SeattleChris/ergo-code/doc/dactyl-motus-6x4-1+3t6.png

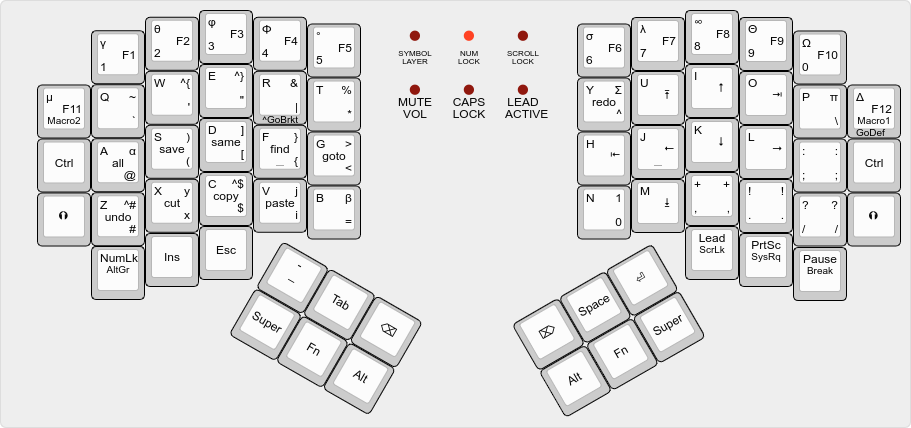
doc/dactyl-motus-6x4-1+3t6.png
