SeattleChris/ergo-code/doc/kb-6col-5row-a.png

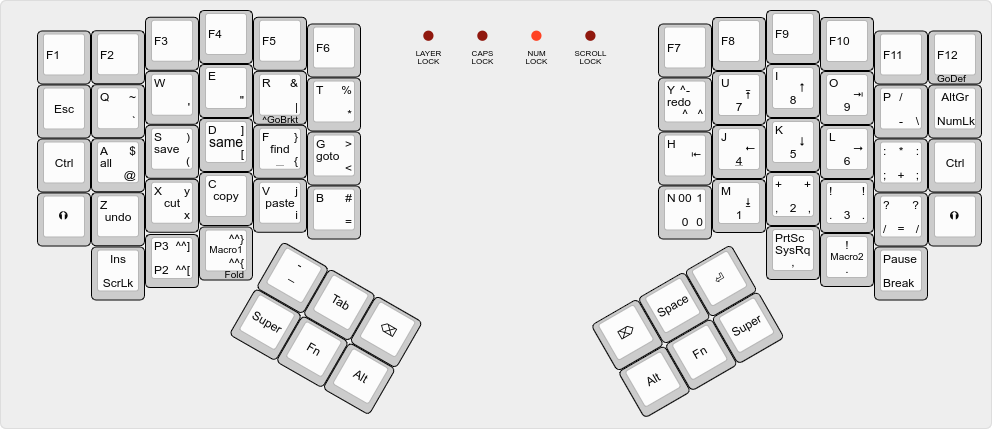
doc/kb-6col-5row-a.png
