SeattleChris/ergo-code/things/test/bowl-4.stl

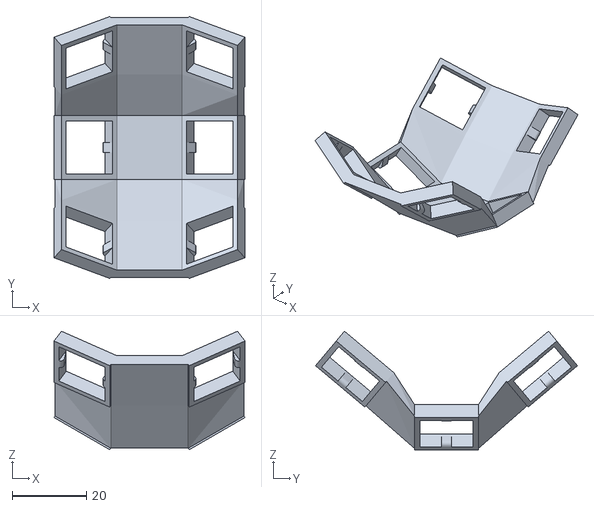
[picture p19: CAD file, 2019-08-27]
things/test/bowl-4.stl
51.5 x 70.7 x 32.0
