SeattleChris/ergo-code/things/chris-2019/right.stl

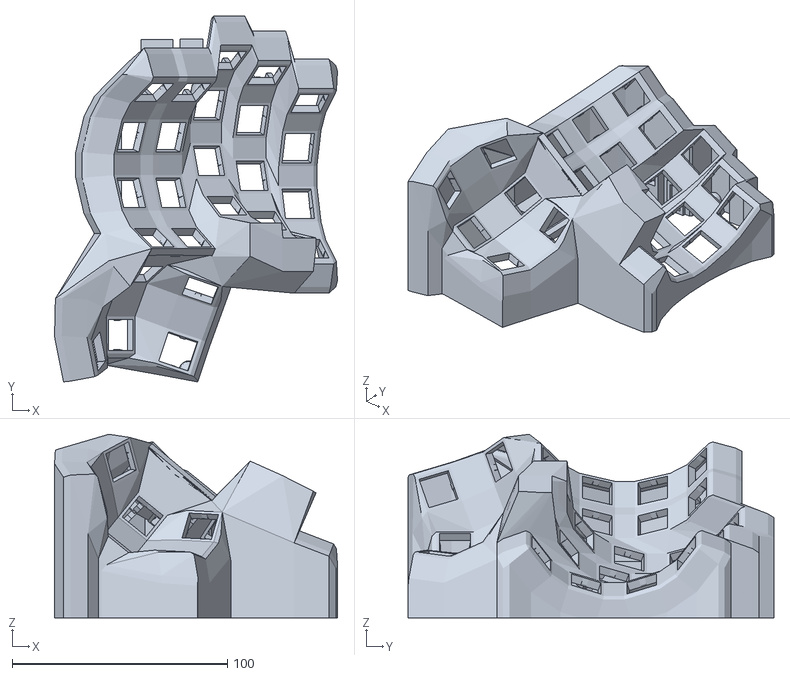
[picture p20: CAD file, 2019-08-27]
things/chris-2019/right.stl
131.4 x 169.8 x 85.2
