SeattleChris/ergo-code/things/right-5x6-plate-ready-to-cut.dxf

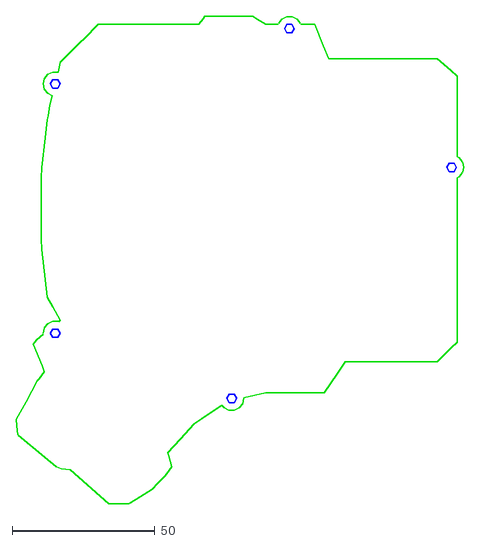
[picture p21: CAD file, 2019-08-27]
things/right-5x6-plate-ready-to-cut.dxf
156.5 x 170.5
