SeattleChris/ergo-code/things/test/thumb-6button.stl

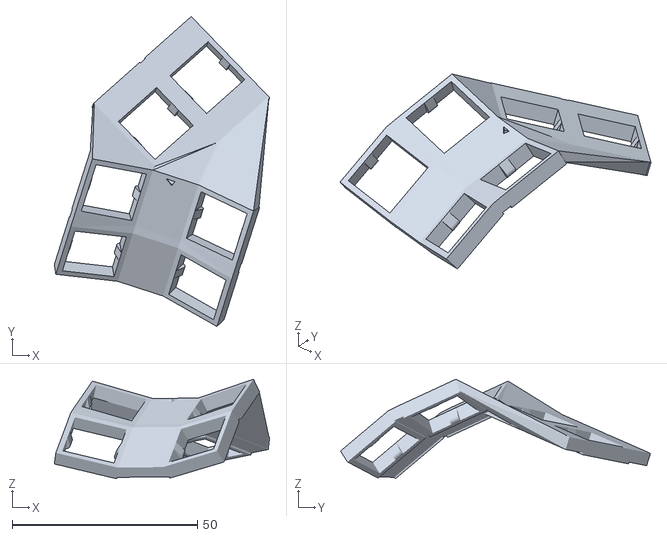
[picture p22: CAD file, 2019-08-27]
things/test/thumb-6button.stl
58.2 x 83.7 x 26.9
