SeattleChris/ergo-code/things/chris-2019/no-num-right.stl

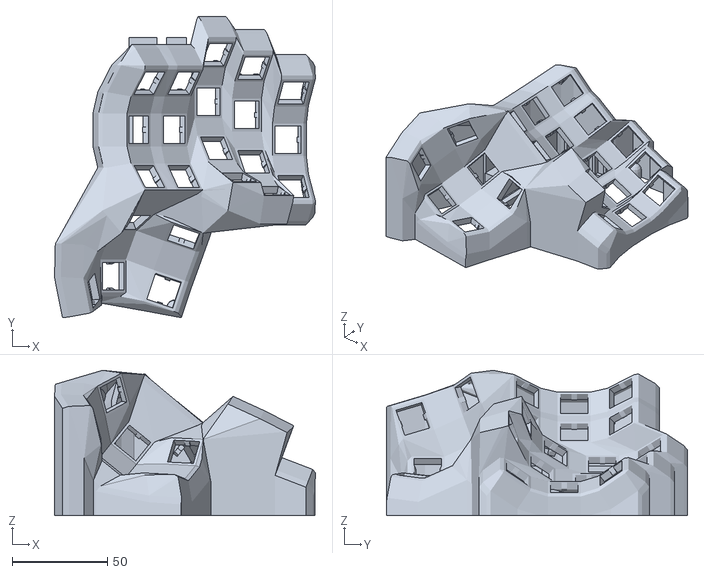
[picture p23: CAD file, 2019-08-27]
things/chris-2019/no-num-right.stl
136.8 x 157.9 x 76.2
