SeattleChris/ergo-code/things/right-4x6.stl

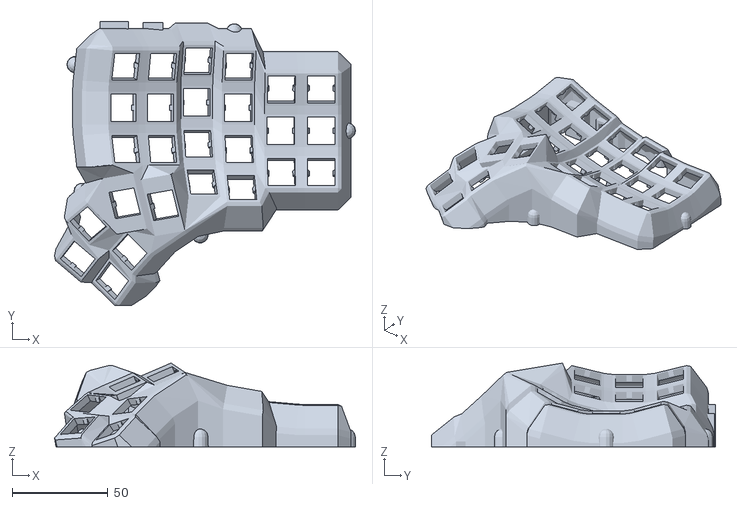
[picture p24: CAD file, 2019-08-27]
things/right-4x6.stl
157.2 x 148.4 x 43.8
