SeattleChris/ergo-code/things/test/thumb-sled1.stl

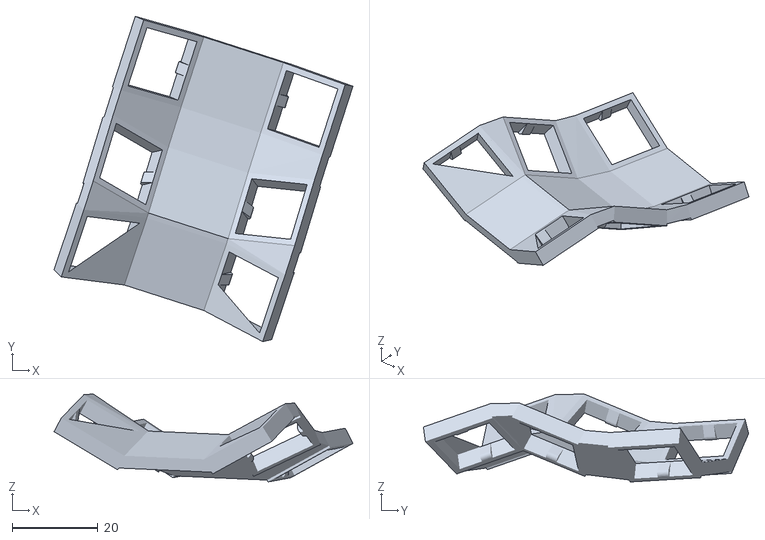
[picture p25: CAD file, 2019-08-27]
things/test/thumb-sled1.stl
69.9 x 76.1 x 20.6
