SeattleChris/ergo-code/things/right-6x6-plate.dxf

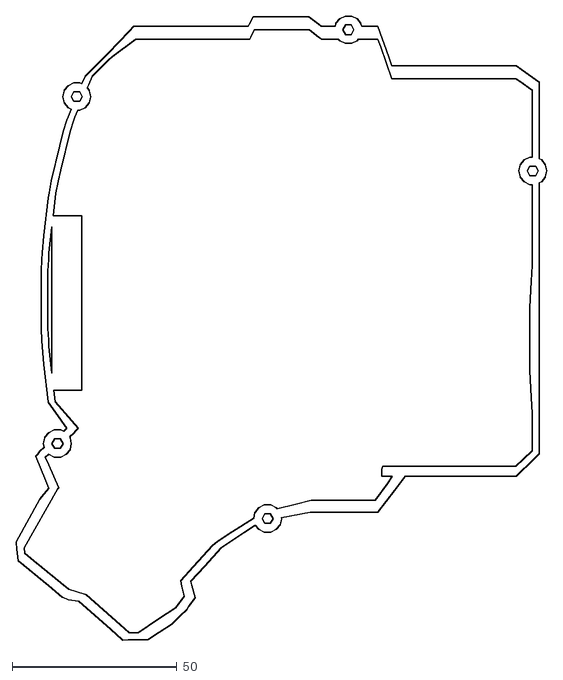
[picture p26: CAD file, 2019-08-27]
things/right-6x6-plate.dxf
160.9 x 189.3
