SeattleChris/ergo-code/things/left-5x6.stl

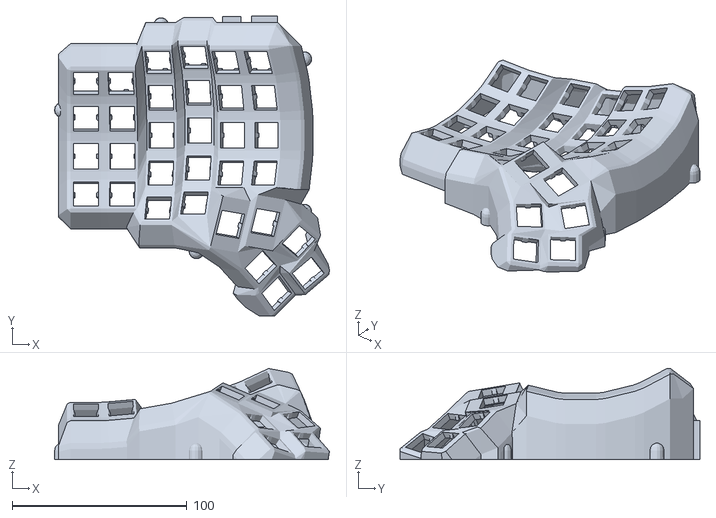
[picture p27: CAD file, 2019-08-27]
things/left-5x6.stl
157.2 x 171.5 x 52.1
