SeattleChris/ergo-code/things/test-lower-thumb.stl

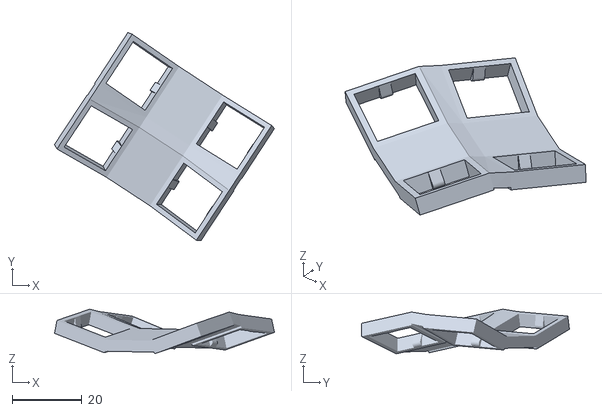
[picture p28: CAD file, 2019-08-27]
things/test-lower-thumb.stl
63.0 x 59.6 x 12.8
