SeattleChris/ergo-code/things/right-4x6-plate.dxf

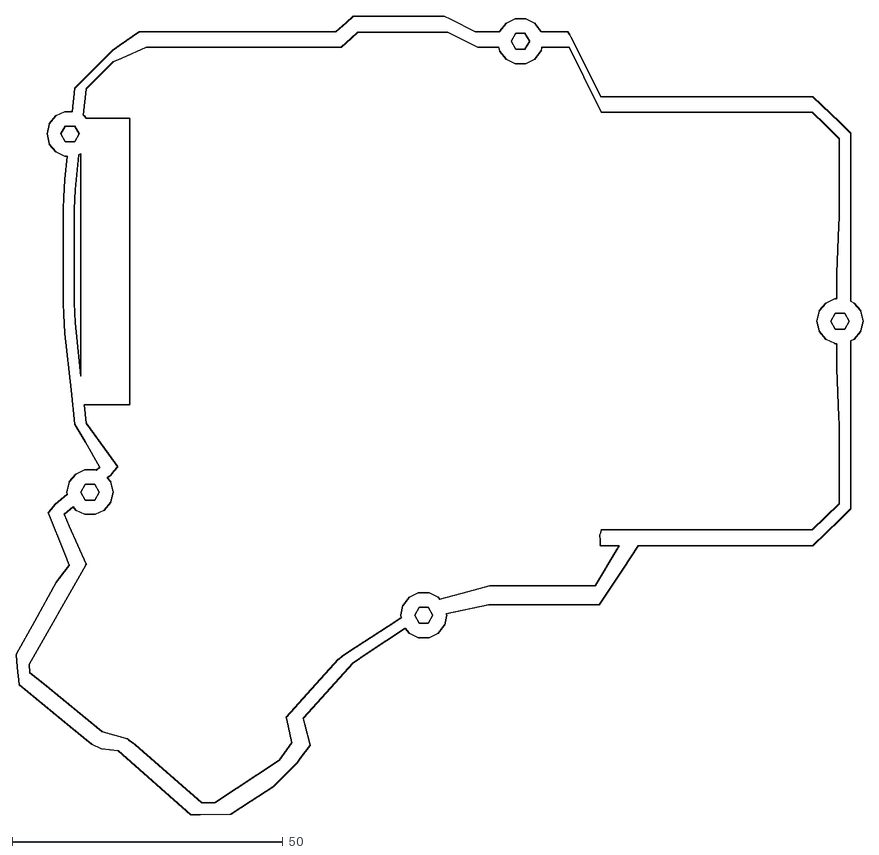
[picture p29: CAD file, 2019-08-27]
things/right-4x6-plate.dxf
156.5 x 147.5
