SeattleChris/ergo-code/things/right-4x5-plate.dxf

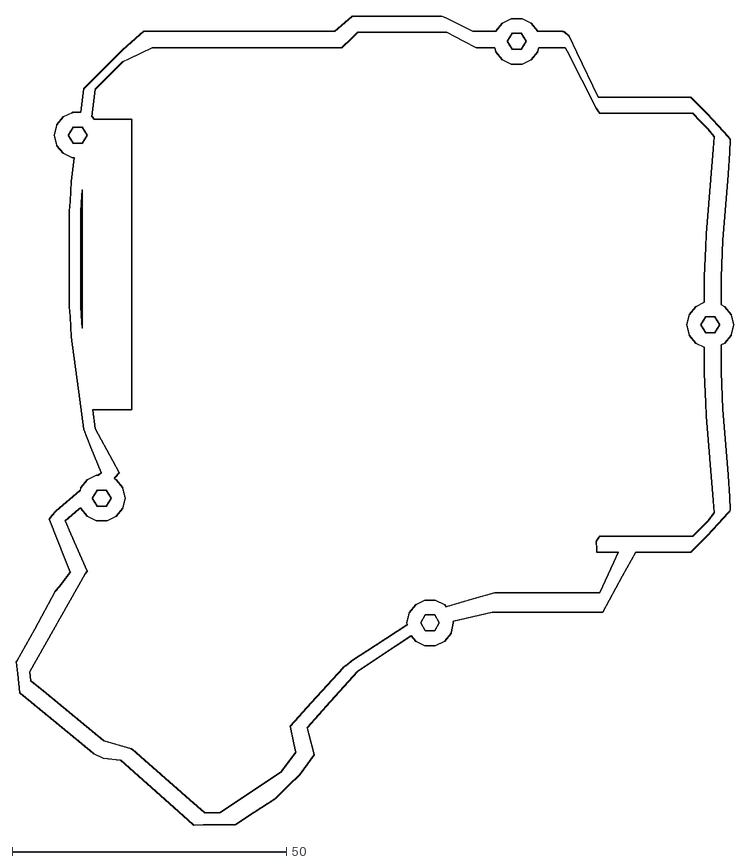
[picture p30: CAD file, 2019-08-27]
things/right-4x5-plate.dxf
130.7 x 147.5
