SeattleChris/ergo-code/things/thumbpad.scad

translate ([0, 0, 8.575]) {
  rotate (a=-40.0, v=[1, 0, 0]) {
    rotate (a=25.0, v=[0, 1, 0]) {
      rotate (a=45.0, v=[0, 0, 1]) {
        rotate (a=-2.5, v=[0, 0, -1]) {
          rotate (a=-59.99999999999999, v=[-1, 0, 0]) {
            rotate (a=-10.0, v=[0, -1, 0]) {
              rotate (a=90.0, v=[0, -1, 0]) {
                rotate (a=90.0, v=[0, 0, 1]) {
                  translate ([35.53437091381005, 63.967580874674, -48.640984358451476]) {
                    union () {
                      union () {
                        union () {
                          translate ([-35.53437091381005, -63.967580874674, 48.640984358451476]) {
                            rotate (a=-2.5, v=[0, 0, 1]) {
                              rotate (a=-10.0, v=[0, 1, 0]) {
                                rotate (a=-59.99999999999999, v=[1, 0, 0]) {
                                  rotate (a=90.0, v=[0, 0, -1]) {
                                    rotate (a=90.0, v=[0, 1, 0]) {
                                      translate ([-8.575, 0, 0]) {
                                        translate ([-9.302129731774905, 0, 0]) {
                                          rotate (a=0.0, v=[1, 0, 0]) {
                                            rotate (a=30.00000000000001, v=[0, 1, 0]) {
                                              union () {
                                                union () {
                                                  translate ([0, 7.825, 1.75]) {
                                                    cube ([17.15, 1.5, 3.5], center=true);
                                                  }
                                                  translate ([7.825, 0, 1.75]) {
                                                    cube ([1.5, 17.15, 3.5], center=true);
                                                  }
                                                  hull () {
                                                    translate ([7.825, 0, 1.75]) {
                                                      cube ([1.5, 2.75, 3.5], center=true);
                                                    }
                                                    translate ([7.075, 0, 1]) {
                                                      rotate (a=90.0, v=[1, 0, 0]) {
                                                        cylinder ($fn=30, h=2.75, r=0, center=true);
                                                      }
                                                    }
                                                  }
                                                }
                                                mirror ([0, 1, 0]) {
                                                  mirror ([1, 0, 0]) {
                                                    union () {
                                                      translate ([0, 7.825, 1.75]) {
                                                        cube ([17.15, 1.5, 3.5], center=true);
                                                      }
                                                      translate ([7.825, 0, 1.75]) {
                                                        cube ([1.5, 17.15, 3.5], center=true);
                                                      }
                                                      hull () {
                                                        translate ([7.825, 0, 1.75]) {
                                                          cube ([1.5, 2.75, 3.5], center=true);
                                                        }
                                                        translate ([7.075, 0, 1]) {
                                                          rotate (a=90.0, v=[1, 0, 0]) {
                                                            cylinder ($fn=30, h=2.75, r=0, center=true);
                                                          }
                                                        }
                                                      }
                                                    }
                                                  }
                                                }
                                              }
                                            }
                                          }
                                        }
                                      }
                                    }
                                  }
                                }
                              }
                            }
                          }
                          translate ([-35.53437091381005, -63.967580874674, 48.640984358451476]) {
                            rotate (a=-2.5, v=[0, 0, 1]) {
                              rotate (a=-10.0, v=[0, 1, 0]) {
                                rotate (a=-59.99999999999999, v=[1, 0, 0]) {
                                  rotate (a=90.0, v=[0, 0, -1]) {
                                    rotate (a=90.0, v=[0, 1, 0]) {
                                      translate ([8.575, 0, 0]) {
                                        translate ([9.302129731774905, 0, 0]) {
                                          rotate (a=0.0, v=[1, 0, 0]) {
                                            rotate (a=30.00000000000001, v=[0, -1, 0]) {
                                              union () {
                                                union () {
                                                  translate ([0, 7.825, 1.75]) {
                                                    cube ([17.15, 1.5, 3.5], center=true);
                                                  }
                                                  translate ([7.825, 0, 1.75]) {
                                                    cube ([1.5, 17.15, 3.5], center=true);
                                                  }
                                                  hull () {
                                                    translate ([7.825, 0, 1.75]) {
                                                      cube ([1.5, 2.75, 3.5], center=true);
                                                    }
                                                    translate ([7.075, 0, 1]) {
                                                      rotate (a=90.0, v=[1, 0, 0]) {
                                                        cylinder ($fn=30, h=2.75, r=0, center=true);
                                                      }
                                                    }
                                                  }
                                                }
                                                mirror ([0, 1, 0]) {
                                                  mirror ([1, 0, 0]) {
                                                    union () {
                                                      translate ([0, 7.825, 1.75]) {
                                                        cube ([17.15, 1.5, 3.5], center=true);
                                                      }
                                                      translate ([7.825, 0, 1.75]) {
                                                        cube ([1.5, 17.15, 3.5], center=true);
                                                      }
                                                      hull () {
                                                        translate ([7.825, 0, 1.75]) {
                                                          cube ([1.5, 2.75, 3.5], center=true);
                                                        }
                                                        translate ([7.075, 0, 1]) {
                                                          rotate (a=90.0, v=[1, 0, 0]) {
                                                            cylinder ($fn=30, h=2.75, r=0, center=true);
                                                          }
                                                        }
                                                      }
                                                    }
                                                  }
                                                }
                                              }
                                            }
                                          }
                                        }
                                      }
                                    }
                                  }
                                }
                              }
                            }
                          }
                          translate ([-35.53437091381005, -63.967580874674, 48.640984358451476]) {
                            rotate (a=-2.5, v=[0, 0, 1]) {
                              rotate (a=-10.0, v=[0, 1, 0]) {
                                rotate (a=-59.99999999999999, v=[1, 0, 0]) {
                                  rotate (a=90.0, v=[0, 0, -1]) {
                                    rotate (a=90.0, v=[0, 1, 0]) {
                                      translate ([0, -13.177145998574055, 15.70391108393905]) {
                                        translate ([-8.575, -12.149999999999999, 0]) {
                                          translate ([-9.302129731774905, 0, 0]) {
                                            rotate (a=-40.0, v=[1, 0, 0]) {
                                              rotate (a=30.00000000000001, v=[0, 1, 0]) {
                                                union () {
                                                  union () {
                                                    translate ([0, 7.825, 1.75]) {
                                                      cube ([17.15, 1.5, 3.5], center=true);
                                                    }
                                                    translate ([7.825, 0, 1.75]) {
                                                      cube ([1.5, 17.15, 3.5], center=true);
                                                    }
                                                    hull () {
                                                      translate ([7.825, 0, 1.75]) {
                                                        cube ([1.5, 2.75, 3.5], center=true);
                                                      }
                                                      translate ([7.075, 0, 1]) {
                                                        rotate (a=90.0, v=[1, 0, 0]) {
                                                          cylinder ($fn=30, h=2.75, r=0, center=true);
                                                        }
                                                      }
                                                    }
                                                  }
                                                  mirror ([0, 1, 0]) {
                                                    mirror ([1, 0, 0]) {
                                                      union () {
                                                        translate ([0, 7.825, 1.75]) {
                                                          cube ([17.15, 1.5, 3.5], center=true);
                                                        }
                                                        translate ([7.825, 0, 1.75]) {
                                                          cube ([1.5, 17.15, 3.5], center=true);
                                                        }
                                                        hull () {
                                                          translate ([7.825, 0, 1.75]) {
                                                            cube ([1.5, 2.75, 3.5], center=true);
                                                          }
                                                          translate ([7.075, 0, 1]) {
                                                            rotate (a=90.0, v=[1, 0, 0]) {
                                                              cylinder ($fn=30, h=2.75, r=0, center=true);
                                                            }
                                                          }
                                                        }
                                                      }
                                                    }
                                                  }
                                                }
                                              }
                                            }
                                          }
                                        }
                                      }
                                    }
                                  }
                                }
                              }
                            }
                          }
                          translate ([-35.53437091381005, -63.967580874674, 48.640984358451476]) {
                            rotate (a=-2.5, v=[0, 0, 1]) {
                              rotate (a=-10.0, v=[0, 1, 0]) {
                                rotate (a=-59.99999999999999, v=[1, 0, 0]) {
                                  rotate (a=90.0, v=[0, 0, -1]) {
                                    rotate (a=90.0, v=[0, 1, 0]) {
                                      translate ([0, -13.177145998574055, 15.70391108393905]) {
                                        translate ([8.575, -12.149999999999999, 0]) {
                                          translate ([9.302129731774905, 0, 0]) {
                                            rotate (a=-40.0, v=[1, 0, 0]) {
                                              rotate (a=30.00000000000001, v=[0, -1, 0]) {
                                                union () {
                                                  union () {
                                                    translate ([0, 7.825, 1.75]) {
                                                      cube ([17.15, 1.5, 3.5], center=true);
                                                    }
                                                    translate ([7.825, 0, 1.75]) {
                                                      cube ([1.5, 17.15, 3.5], center=true);
                                                    }
                                                    hull () {
                                                      translate ([7.825, 0, 1.75]) {
                                                        cube ([1.5, 2.75, 3.5], center=true);
                                                      }
                                                      translate ([7.075, 0, 1]) {
                                                        rotate (a=90.0, v=[1, 0, 0]) {
                                                          cylinder ($fn=30, h=2.75, r=0, center=true);
                                                        }
                                                      }
                                                    }
                                                  }
                                                  mirror ([0, 1, 0]) {
                                                    mirror ([1, 0, 0]) {
                                                      union () {
                                                        translate ([0, 7.825, 1.75]) {
                                                          cube ([17.15, 1.5, 3.5], center=true);
                                                        }
                                                        translate ([7.825, 0, 1.75]) {
                                                          cube ([1.5, 17.15, 3.5], center=true);
                                                        }
                                                        hull () {
                                                          translate ([7.825, 0, 1.75]) {
                                                            cube ([1.5, 2.75, 3.5], center=true);
                                                          }
                                                          translate ([7.075, 0, 1]) {
                                                            rotate (a=90.0, v=[1, 0, 0]) {
                                                              cylinder ($fn=30, h=2.75, r=0, center=true);
                                                            }
                                                          }
                                                        }
                                                      }
                                                    }
                                                  }
                                                }
                                              }
                                            }
                                          }
                                        }
                                      }
                                    }
                                  }
                                }
                              }
                            }
                          }
                        }
                        union () {
                          translate ([-35.53437091381005, -63.967580874674, 48.640984358451476]) {
                            rotate (a=-2.5, v=[0, 0, 1]) {
                              rotate (a=-10.0, v=[0, 1, 0]) {
                                rotate (a=-59.99999999999999, v=[1, 0, 0]) {
                                  rotate (a=90.0, v=[0, 0, -1]) {
                                    rotate (a=90.0, v=[0, 1, 0]) {
                                      translate ([0, 13.177145998574055, 15.70391108393905]) {
                                        translate ([-8.575, 12.149999999999999, 0]) {
                                          translate ([-9.302129731774905, 0, 0]) {
                                            rotate (a=40.0, v=[1, 0, 0]) {
                                              rotate (a=30.00000000000001, v=[0, 1, 0]) {
                                                union () {
                                                  union () {
                                                    translate ([0, 7.825, 1.75]) {
                                                      cube ([17.15, 1.5, 3.5], center=true);
                                                    }
                                                    translate ([7.825, 0, 1.75]) {
                                                      cube ([1.5, 17.15, 3.5], center=true);
                                                    }
                                                    hull () {
                                                      translate ([7.825, 0, 1.75]) {
                                                        cube ([1.5, 2.75, 3.5], center=true);
                                                      }
                                                      translate ([7.075, 0, 1]) {
                                                        rotate (a=90.0, v=[1, 0, 0]) {
                                                          cylinder ($fn=30, h=2.75, r=0, center=true);
                                                        }
                                                      }
                                                    }
                                                  }
                                                  mirror ([0, 1, 0]) {
                                                    mirror ([1, 0, 0]) {
                                                      union () {
                                                        translate ([0, 7.825, 1.75]) {
                                                          cube ([17.15, 1.5, 3.5], center=true);
                                                        }
                                                        translate ([7.825, 0, 1.75]) {
                                                          cube ([1.5, 17.15, 3.5], center=true);
                                                        }
                                                        hull () {
                                                          translate ([7.825, 0, 1.75]) {
                                                            cube ([1.5, 2.75, 3.5], center=true);
                                                          }
                                                          translate ([7.075, 0, 1]) {
                                                            rotate (a=90.0, v=[1, 0, 0]) {
                                                              cylinder ($fn=30, h=2.75, r=0, center=true);
                                                            }
                                                          }
                                                        }
                                                      }
                                                    }
                                                  }
                                                }
                                              }
                                            }
                                          }
                                        }
                                      }
                                    }
                                  }
                                }
                              }
                            }
                          }
                          translate ([-35.53437091381005, -63.967580874674, 48.640984358451476]) {
                            rotate (a=-2.5, v=[0, 0, 1]) {
                              rotate (a=-10.0, v=[0, 1, 0]) {
                                rotate (a=-59.99999999999999, v=[1, 0, 0]) {
                                  rotate (a=90.0, v=[0, 0, -1]) {
                                    rotate (a=90.0, v=[0, 1, 0]) {
                                      translate ([0, 13.177145998574055, 15.70391108393905]) {
                                        translate ([8.575, 12.149999999999999, 0]) {
                                          translate ([9.302129731774905, 0, 0]) {
                                            rotate (a=40.0, v=[1, 0, 0]) {
                                              rotate (a=30.00000000000001, v=[0, -1, 0]) {
                                                union () {
                                                  union () {
                                                    translate ([0, 7.825, 1.75]) {
                                                      cube ([17.15, 1.5, 3.5], center=true);
                                                    }
                                                    translate ([7.825, 0, 1.75]) {
                                                      cube ([1.5, 17.15, 3.5], center=true);
                                                    }
                                                    hull () {
                                                      translate ([7.825, 0, 1.75]) {
                                                        cube ([1.5, 2.75, 3.5], center=true);
                                                      }
                                                      translate ([7.075, 0, 1]) {
                                                        rotate (a=90.0, v=[1, 0, 0]) {
                                                          cylinder ($fn=30, h=2.75, r=0, center=true);
                                                        }
                                                      }
                                                    }
                                                  }
                                                  mirror ([0, 1, 0]) {
                                                    mirror ([1, 0, 0]) {
                                                      union () {
                                                        translate ([0, 7.825, 1.75]) {
                                                          cube ([17.15, 1.5, 3.5], center=true);
                                                        }
                                                        translate ([7.825, 0, 1.75]) {
                                                          cube ([1.5, 17.15, 3.5], center=true);
                                                        }
                                                        hull () {
                                                          translate ([7.825, 0, 1.75]) {
                                                            cube ([1.5, 2.75, 3.5], center=true);
                                                          }
                                                          translate ([7.075, 0, 1]) {
                                                            rotate (a=90.0, v=[1, 0, 0]) {
                                                              cylinder ($fn=30, h=2.75, r=0, center=true);
                                                            }
                                                          }
                                                        }
                                                      }
                                                    }
                                                  }
                                                }
                                              }
                                            }
                                          }
                                        }
                                      }
                                    }
                                  }
                                }
                              }
                            }
                          }
                        }
                      }
                      union () {
                        union () {
                          hull () {
                            translate ([-35.53437091381005, -63.967580874674, 48.640984358451476]) {
                              rotate (a=-2.5, v=[0, 0, 1]) {
                                rotate (a=-10.0, v=[0, 1, 0]) {
                                  rotate (a=-59.99999999999999, v=[1, 0, 0]) {
                                    rotate (a=90.0, v=[0, 0, -1]) {
                                      rotate (a=90.0, v=[0, 1, 0]) {
                                        translate ([0, 13.177145998574055, 15.70391108393905]) {
                                          translate ([-8.575, 12.149999999999999, 0]) {
                                            translate ([-9.302129731774905, 0, 0]) {
                                              rotate (a=40.0, v=[1, 0, 0]) {
                                                rotate (a=30.00000000000001, v=[0, 1, 0]) {
                                                  translate ([8.524999999999999, 8.524999999999999, 0]) {
                                                    translate ([0, 0, 1.75]) {
                                                      cube ([0.1, 0.1, 3.5], center=true);
                                                    }
                                                  }
                                                }
                                              }
                                            }
                                          }
                                        }
                                      }
                                    }
                                  }
                                }
                              }
                            }
                            translate ([-35.53437091381005, -63.967580874674, 48.640984358451476]) {
                              rotate (a=-2.5, v=[0, 0, 1]) {
                                rotate (a=-10.0, v=[0, 1, 0]) {
                                  rotate (a=-59.99999999999999, v=[1, 0, 0]) {
                                    rotate (a=90.0, v=[0, 0, -1]) {
                                      rotate (a=90.0, v=[0, 1, 0]) {
                                        translate ([0, 13.177145998574055, 15.70391108393905]) {
                                          translate ([8.575, 12.149999999999999, 0]) {
                                            translate ([9.302129731774905, 0, 0]) {
                                              rotate (a=40.0, v=[1, 0, 0]) {
                                                rotate (a=30.00000000000001, v=[0, -1, 0]) {
                                                  translate ([-8.524999999999999, 8.524999999999999, 0]) {
                                                    translate ([0, 0, 1.75]) {
                                                      cube ([0.1, 0.1, 3.5], center=true);
                                                    }
                                                  }
                                                }
                                              }
                                            }
                                          }
                                        }
                                      }
                                    }
                                  }
                                }
                              }
                            }
                            translate ([-35.53437091381005, -63.967580874674, 48.640984358451476]) {
                              rotate (a=-2.5, v=[0, 0, 1]) {
                                rotate (a=-10.0, v=[0, 1, 0]) {
                                  rotate (a=-59.99999999999999, v=[1, 0, 0]) {
                                    rotate (a=90.0, v=[0, 0, -1]) {
                                      rotate (a=90.0, v=[0, 1, 0]) {
                                        translate ([0, 13.177145998574055, 15.70391108393905]) {
                                          translate ([-8.575, 12.149999999999999, 0]) {
                                            translate ([-9.302129731774905, 0, 0]) {
                                              rotate (a=40.0, v=[1, 0, 0]) {
                                                rotate (a=30.00000000000001, v=[0, 1, 0]) {
                                                  translate ([8.524999999999999, -8.524999999999999, 0]) {
                                                    translate ([0, 0, 1.75]) {
                                                      cube ([0.1, 0.1, 3.5], center=true);
                                                    }
                                                  }
                                                }
                                              }
                                            }
                                          }
                                        }
                                      }
                                    }
                                  }
                                }
                              }
                            }
                          }
                          hull () {
                            translate ([-35.53437091381005, -63.967580874674, 48.640984358451476]) {
                              rotate (a=-2.5, v=[0, 0, 1]) {
                                rotate (a=-10.0, v=[0, 1, 0]) {
                                  rotate (a=-59.99999999999999, v=[1, 0, 0]) {
                                    rotate (a=90.0, v=[0, 0, -1]) {
                                      rotate (a=90.0, v=[0, 1, 0]) {
                                        translate ([0, 13.177145998574055, 15.70391108393905]) {
                                          translate ([8.575, 12.149999999999999, 0]) {
                                            translate ([9.302129731774905, 0, 0]) {
                                              rotate (a=40.0, v=[1, 0, 0]) {
                                                rotate (a=30.00000000000001, v=[0, -1, 0]) {
                                                  translate ([-8.524999999999999, 8.524999999999999, 0]) {
                                                    translate ([0, 0, 1.75]) {
                                                      cube ([0.1, 0.1, 3.5], center=true);
                                                    }
                                                  }
                                                }
                                              }
                                            }
                                          }
                                        }
                                      }
                                    }
                                  }
                                }
                              }
                            }
                            translate ([-35.53437091381005, -63.967580874674, 48.640984358451476]) {
                              rotate (a=-2.5, v=[0, 0, 1]) {
                                rotate (a=-10.0, v=[0, 1, 0]) {
                                  rotate (a=-59.99999999999999, v=[1, 0, 0]) {
                                    rotate (a=90.0, v=[0, 0, -1]) {
                                      rotate (a=90.0, v=[0, 1, 0]) {
                                        translate ([0, 13.177145998574055, 15.70391108393905]) {
                                          translate ([-8.575, 12.149999999999999, 0]) {
                                            translate ([-9.302129731774905, 0, 0]) {
                                              rotate (a=40.0, v=[1, 0, 0]) {
                                                rotate (a=30.00000000000001, v=[0, 1, 0]) {
                                                  translate ([8.524999999999999, -8.524999999999999, 0]) {
                                                    translate ([0, 0, 1.75]) {
                                                      cube ([0.1, 0.1, 3.5], center=true);
                                                    }
                                                  }
                                                }
                                              }
                                            }
                                          }
                                        }
                                      }
                                    }
                                  }
                                }
                              }
                            }
                            translate ([-35.53437091381005, -63.967580874674, 48.640984358451476]) {
                              rotate (a=-2.5, v=[0, 0, 1]) {
                                rotate (a=-10.0, v=[0, 1, 0]) {
                                  rotate (a=-59.99999999999999, v=[1, 0, 0]) {
                                    rotate (a=90.0, v=[0, 0, -1]) {
                                      rotate (a=90.0, v=[0, 1, 0]) {
                                        translate ([0, 13.177145998574055, 15.70391108393905]) {
                                          translate ([8.575, 12.149999999999999, 0]) {
                                            translate ([9.302129731774905, 0, 0]) {
                                              rotate (a=40.0, v=[1, 0, 0]) {
                                                rotate (a=30.00000000000001, v=[0, -1, 0]) {
                                                  translate ([-8.524999999999999, -8.524999999999999, 0]) {
                                                    translate ([0, 0, 1.75]) {
                                                      cube ([0.1, 0.1, 3.5], center=true);
                                                    }
                                                  }
                                                }
                                              }
                                            }
                                          }
                                        }
                                      }
                                    }
                                  }
                                }
                              }
                            }
                          }
                        }
                        union () {
                          hull () {
                            translate ([-35.53437091381005, -63.967580874674, 48.640984358451476]) {
                              rotate (a=-2.5, v=[0, 0, 1]) {
                                rotate (a=-10.0, v=[0, 1, 0]) {
                                  rotate (a=-59.99999999999999, v=[1, 0, 0]) {
                                    rotate (a=90.0, v=[0, 0, -1]) {
                                      rotate (a=90.0, v=[0, 1, 0]) {
                                        translate ([0, -13.177145998574055, 15.70391108393905]) {
                                          translate ([8.575, -12.149999999999999, 0]) {
                                            translate ([9.302129731774905, 0, 0]) {
                                              rotate (a=-40.0, v=[1, 0, 0]) {
                                                rotate (a=30.00000000000001, v=[0, -1, 0]) {
                                                  translate ([-8.524999999999999, -8.524999999999999, 0]) {
                                                    translate ([0, 0, 1.75]) {
                                                      cube ([0.1, 0.1, 3.5], center=true);
                                                    }
                                                  }
                                                }
                                              }
                                            }
                                          }
                                        }
                                      }
                                    }
                                  }
                                }
                              }
                            }
                            translate ([-35.53437091381005, -63.967580874674, 48.640984358451476]) {
                              rotate (a=-2.5, v=[0, 0, 1]) {
                                rotate (a=-10.0, v=[0, 1, 0]) {
                                  rotate (a=-59.99999999999999, v=[1, 0, 0]) {
                                    rotate (a=90.0, v=[0, 0, -1]) {
                                      rotate (a=90.0, v=[0, 1, 0]) {
                                        translate ([0, -13.177145998574055, 15.70391108393905]) {
                                          translate ([-8.575, -12.149999999999999, 0]) {
                                            translate ([-9.302129731774905, 0, 0]) {
                                              rotate (a=-40.0, v=[1, 0, 0]) {
                                                rotate (a=30.00000000000001, v=[0, 1, 0]) {
                                                  translate ([8.524999999999999, -8.524999999999999, 0]) {
                                                    translate ([0, 0, 1.75]) {
                                                      cube ([0.1, 0.1, 3.5], center=true);
                                                    }
                                                  }
                                                }
                                              }
                                            }
                                          }
                                        }
                                      }
                                    }
                                  }
                                }
                              }
                            }
                            translate ([-35.53437091381005, -63.967580874674, 48.640984358451476]) {
                              rotate (a=-2.5, v=[0, 0, 1]) {
                                rotate (a=-10.0, v=[0, 1, 0]) {
                                  rotate (a=-59.99999999999999, v=[1, 0, 0]) {
                                    rotate (a=90.0, v=[0, 0, -1]) {
                                      rotate (a=90.0, v=[0, 1, 0]) {
                                        translate ([0, -13.177145998574055, 15.70391108393905]) {
                                          translate ([8.575, -12.149999999999999, 0]) {
                                            translate ([9.302129731774905, 0, 0]) {
                                              rotate (a=-40.0, v=[1, 0, 0]) {
                                                rotate (a=30.00000000000001, v=[0, -1, 0]) {
                                                  translate ([-8.524999999999999, 8.524999999999999, 0]) {
                                                    translate ([0, 0, 1.75]) {
                                                      cube ([0.1, 0.1, 3.5], center=true);
                                                    }
                                                  }
                                                }
                                              }
                                            }
                                          }
                                        }
                                      }
                                    }
                                  }
                                }
                              }
                            }
                          }
                          hull () {
                            translate ([-35.53437091381005, -63.967580874674, 48.640984358451476]) {
                              rotate (a=-2.5, v=[0, 0, 1]) {
                                rotate (a=-10.0, v=[0, 1, 0]) {
                                  rotate (a=-59.99999999999999, v=[1, 0, 0]) {
                                    rotate (a=90.0, v=[0, 0, -1]) {
                                      rotate (a=90.0, v=[0, 1, 0]) {
                                        translate ([0, -13.177145998574055, 15.70391108393905]) {
                                          translate ([-8.575, -12.149999999999999, 0]) {
                                            translate ([-9.302129731774905, 0, 0]) {
                                              rotate (a=-40.0, v=[1, 0, 0]) {
                                                rotate (a=30.00000000000001, v=[0, 1, 0]) {
                                                  translate ([8.524999999999999, -8.524999999999999, 0]) {
                                                    translate ([0, 0, 1.75]) {
                                                      cube ([0.1, 0.1, 3.5], center=true);
                                                    }
                                                  }
                                                }
                                              }
                                            }
                                          }
                                        }
                                      }
                                    }
                                  }
                                }
                              }
                            }
                            translate ([-35.53437091381005, -63.967580874674, 48.640984358451476]) {
                              rotate (a=-2.5, v=[0, 0, 1]) {
                                rotate (a=-10.0, v=[0, 1, 0]) {
                                  rotate (a=-59.99999999999999, v=[1, 0, 0]) {
                                    rotate (a=90.0, v=[0, 0, -1]) {
                                      rotate (a=90.0, v=[0, 1, 0]) {
                                        translate ([0, -13.177145998574055, 15.70391108393905]) {
                                          translate ([8.575, -12.149999999999999, 0]) {
                                            translate ([9.302129731774905, 0, 0]) {
                                              rotate (a=-40.0, v=[1, 0, 0]) {
                                                rotate (a=30.00000000000001, v=[0, -1, 0]) {
                                                  translate ([-8.524999999999999, 8.524999999999999, 0]) {
                                                    translate ([0, 0, 1.75]) {
                                                      cube ([0.1, 0.1, 3.5], center=true);
                                                    }
                                                  }
                                                }
                                              }
                                            }
                                          }
                                        }
                                      }
                                    }
                                  }
                                }
                              }
                            }
                            translate ([-35.53437091381005, -63.967580874674, 48.640984358451476]) {
                              rotate (a=-2.5, v=[0, 0, 1]) {
                                rotate (a=-10.0, v=[0, 1, 0]) {
                                  rotate (a=-59.99999999999999, v=[1, 0, 0]) {
                                    rotate (a=90.0, v=[0, 0, -1]) {
                                      rotate (a=90.0, v=[0, 1, 0]) {
                                        translate ([0, -13.177145998574055, 15.70391108393905]) {
                                          translate ([-8.575, -12.149999999999999, 0]) {
                                            translate ([-9.302129731774905, 0, 0]) {
                                              rotate (a=-40.0, v=[1, 0, 0]) {
                                                rotate (a=30.00000000000001, v=[0, 1, 0]) {
                                                  translate ([8.524999999999999, 8.524999999999999, 0]) {
                                                    translate ([0, 0, 1.75]) {
                                                      cube ([0.1, 0.1, 3.5], center=true);
                                                    }
                                                  }
                                                }
                                              }
                                            }
                                          }
                                        }
                                      }
                                    }
                                  }
                                }
                              }
                            }
                          }
                          hull () {
                            translate ([-35.53437091381005, -63.967580874674, 48.640984358451476]) {
                              rotate (a=-2.5, v=[0, 0, 1]) {
                                rotate (a=-10.0, v=[0, 1, 0]) {
                                  rotate (a=-59.99999999999999, v=[1, 0, 0]) {
                                    rotate (a=90.0, v=[0, 0, -1]) {
                                      rotate (a=90.0, v=[0, 1, 0]) {
                                        translate ([0, -13.177145998574055, 15.70391108393905]) {
                                          translate ([8.575, -12.149999999999999, 0]) {
                                            translate ([9.302129731774905, 0, 0]) {
                                              rotate (a=-40.0, v=[1, 0, 0]) {
                                                rotate (a=30.00000000000001, v=[0, -1, 0]) {
                                                  translate ([-8.524999999999999, 8.524999999999999, 0]) {
                                                    translate ([0, 0, 1.75]) {
                                                      cube ([0.1, 0.1, 3.5], center=true);
                                                    }
                                                  }
                                                }
                                              }
                                            }
                                          }
                                        }
                                      }
                                    }
                                  }
                                }
                              }
                            }
                            translate ([-35.53437091381005, -63.967580874674, 48.640984358451476]) {
                              rotate (a=-2.5, v=[0, 0, 1]) {
                                rotate (a=-10.0, v=[0, 1, 0]) {
                                  rotate (a=-59.99999999999999, v=[1, 0, 0]) {
                                    rotate (a=90.0, v=[0, 0, -1]) {
                                      rotate (a=90.0, v=[0, 1, 0]) {
                                        translate ([0, -13.177145998574055, 15.70391108393905]) {
                                          translate ([-8.575, -12.149999999999999, 0]) {
                                            translate ([-9.302129731774905, 0, 0]) {
                                              rotate (a=-40.0, v=[1, 0, 0]) {
                                                rotate (a=30.00000000000001, v=[0, 1, 0]) {
                                                  translate ([8.524999999999999, 8.524999999999999, 0]) {
                                                    translate ([0, 0, 1.75]) {
                                                      cube ([0.1, 0.1, 3.5], center=true);
                                                    }
                                                  }
                                                }
                                              }
                                            }
                                          }
                                        }
                                      }
                                    }
                                  }
                                }
                              }
                            }
                            translate ([-35.53437091381005, -63.967580874674, 48.640984358451476]) {
                              rotate (a=-2.5, v=[0, 0, 1]) {
                                rotate (a=-10.0, v=[0, 1, 0]) {
                                  rotate (a=-59.99999999999999, v=[1, 0, 0]) {
                                    rotate (a=90.0, v=[0, 0, -1]) {
                                      rotate (a=90.0, v=[0, 1, 0]) {
                                        translate ([8.575, 0, 0]) {
                                          translate ([9.302129731774905, 0, 0]) {
                                            rotate (a=0.0, v=[1, 0, 0]) {
                                              rotate (a=30.00000000000001, v=[0, -1, 0]) {
                                                translate ([-8.524999999999999, -8.524999999999999, 0]) {
                                                  translate ([0, 0, 1.75]) {
                                                    cube ([0.1, 0.1, 3.5], center=true);
                                                  }
                                                }
                                              }
                                            }
                                          }
                                        }
                                      }
                                    }
                                  }
                                }
                              }
                            }
                          }
                          hull () {
                            translate ([-35.53437091381005, -63.967580874674, 48.640984358451476]) {
                              rotate (a=-2.5, v=[0, 0, 1]) {
                                rotate (a=-10.0, v=[0, 1, 0]) {
                                  rotate (a=-59.99999999999999, v=[1, 0, 0]) {
                                    rotate (a=90.0, v=[0, 0, -1]) {
                                      rotate (a=90.0, v=[0, 1, 0]) {
                                        translate ([0, -13.177145998574055, 15.70391108393905]) {
                                          translate ([-8.575, -12.149999999999999, 0]) {
                                            translate ([-9.302129731774905, 0, 0]) {
                                              rotate (a=-40.0, v=[1, 0, 0]) {
                                                rotate (a=30.00000000000001, v=[0, 1, 0]) {
                                                  translate ([8.524999999999999, 8.524999999999999, 0]) {
                                                    translate ([0, 0, 1.75]) {
                                                      cube ([0.1, 0.1, 3.5], center=true);
                                                    }
                                                  }
                                                }
                                              }
                                            }
                                          }
                                        }
                                      }
                                    }
                                  }
                                }
                              }
                            }
                            translate ([-35.53437091381005, -63.967580874674, 48.640984358451476]) {
                              rotate (a=-2.5, v=[0, 0, 1]) {
                                rotate (a=-10.0, v=[0, 1, 0]) {
                                  rotate (a=-59.99999999999999, v=[1, 0, 0]) {
                                    rotate (a=90.0, v=[0, 0, -1]) {
                                      rotate (a=90.0, v=[0, 1, 0]) {
                                        translate ([8.575, 0, 0]) {
                                          translate ([9.302129731774905, 0, 0]) {
                                            rotate (a=0.0, v=[1, 0, 0]) {
                                              rotate (a=30.00000000000001, v=[0, -1, 0]) {
                                                translate ([-8.524999999999999, -8.524999999999999, 0]) {
                                                  translate ([0, 0, 1.75]) {
                                                    cube ([0.1, 0.1, 3.5], center=true);
                                                  }
                                                }
                                              }
                                            }
                                          }
                                        }
                                      }
                                    }
                                  }
                                }
                              }
                            }
                            translate ([-35.53437091381005, -63.967580874674, 48.640984358451476]) {
                              rotate (a=-2.5, v=[0, 0, 1]) {
                                rotate (a=-10.0, v=[0, 1, 0]) {
                                  rotate (a=-59.99999999999999, v=[1, 0, 0]) {
                                    rotate (a=90.0, v=[0, 0, -1]) {
                                      rotate (a=90.0, v=[0, 1, 0]) {
                                        translate ([-8.575, 0, 0]) {
                                          translate ([-9.302129731774905, 0, 0]) {
                                            rotate (a=0.0, v=[1, 0, 0]) {
                                              rotate (a=30.00000000000001, v=[0, 1, 0]) {
                                                translate ([8.524999999999999, -8.524999999999999, 0]) {
                                                  translate ([0, 0, 1.75]) {
                                                    cube ([0.1, 0.1, 3.5], center=true);
                                                  }
                                                }
                                              }
                                            }
                                          }
                                        }
                                      }
                                    }
                                  }
                                }
                              }
                            }
                          }
                          hull () {
                            translate ([-35.53437091381005, -63.967580874674, 48.640984358451476]) {
                              rotate (a=-2.5, v=[0, 0, 1]) {
                                rotate (a=-10.0, v=[0, 1, 0]) {
                                  rotate (a=-59.99999999999999, v=[1, 0, 0]) {
                                    rotate (a=90.0, v=[0, 0, -1]) {
                                      rotate (a=90.0, v=[0, 1, 0]) {
                                        translate ([8.575, 0, 0]) {
                                          translate ([9.302129731774905, 0, 0]) {
                                            rotate (a=0.0, v=[1, 0, 0]) {
                                              rotate (a=30.00000000000001, v=[0, -1, 0]) {
                                                translate ([-8.524999999999999, -8.524999999999999, 0]) {
                                                  translate ([0, 0, 1.75]) {
                                                    cube ([0.1, 0.1, 3.5], center=true);
                                                  }
                                                }
                                              }
                                            }
                                          }
                                        }
                                      }
                                    }
                                  }
                                }
                              }
                            }
                            translate ([-35.53437091381005, -63.967580874674, 48.640984358451476]) {
                              rotate (a=-2.5, v=[0, 0, 1]) {
                                rotate (a=-10.0, v=[0, 1, 0]) {
                                  rotate (a=-59.99999999999999, v=[1, 0, 0]) {
                                    rotate (a=90.0, v=[0, 0, -1]) {
                                      rotate (a=90.0, v=[0, 1, 0]) {
                                        translate ([-8.575, 0, 0]) {
                                          translate ([-9.302129731774905, 0, 0]) {
                                            rotate (a=0.0, v=[1, 0, 0]) {
                                              rotate (a=30.00000000000001, v=[0, 1, 0]) {
                                                translate ([8.524999999999999, -8.524999999999999, 0]) {
                                                  translate ([0, 0, 1.75]) {
                                                    cube ([0.1, 0.1, 3.5], center=true);
                                                  }
                                                }
                                              }
                                            }
                                          }
                                        }
                                      }
                                    }
                                  }
                                }
                              }
                            }
                            translate ([-35.53437091381005, -63.967580874674, 48.640984358451476]) {
                              rotate (a=-2.5, v=[0, 0, 1]) {
                                rotate (a=-10.0, v=[0, 1, 0]) {
                                  rotate (a=-59.99999999999999, v=[1, 0, 0]) {
                                    rotate (a=90.0, v=[0, 0, -1]) {
                                      rotate (a=90.0, v=[0, 1, 0]) {
                                        translate ([8.575, 0, 0]) {
                                          translate ([9.302129731774905, 0, 0]) {
                                            rotate (a=0.0, v=[1, 0, 0]) {
                                              rotate (a=30.00000000000001, v=[0, -1, 0]) {
                                                translate ([-8.524999999999999, 8.524999999999999, 0]) {
                                                  translate ([0, 0, 1.75]) {
                                                    cube ([0.1, 0.1, 3.5], center=true);
                                                  }
                                                }
                                              }
                                            }
                                          }
                                        }
                                      }
                                    }
                                  }
                                }
                              }
                            }
                          }
                          hull () {
                            translate ([-35.53437091381005, -63.967580874674, 48.640984358451476]) {
                              rotate (a=-2.5, v=[0, 0, 1]) {
                                rotate (a=-10.0, v=[0, 1, 0]) {
                                  rotate (a=-59.99999999999999, v=[1, 0, 0]) {
                                    rotate (a=90.0, v=[0, 0, -1]) {
                                      rotate (a=90.0, v=[0, 1, 0]) {
                                        translate ([-8.575, 0, 0]) {
                                          translate ([-9.302129731774905, 0, 0]) {
                                            rotate (a=0.0, v=[1, 0, 0]) {
                                              rotate (a=30.00000000000001, v=[0, 1, 0]) {
                                                translate ([8.524999999999999, -8.524999999999999, 0]) {
                                                  translate ([0, 0, 1.75]) {
                                                    cube ([0.1, 0.1, 3.5], center=true);
                                                  }
                                                }
                                              }
                                            }
                                          }
                                        }
                                      }
                                    }
                                  }
                                }
                              }
                            }
                            translate ([-35.53437091381005, -63.967580874674, 48.640984358451476]) {
                              rotate (a=-2.5, v=[0, 0, 1]) {
                                rotate (a=-10.0, v=[0, 1, 0]) {
                                  rotate (a=-59.99999999999999, v=[1, 0, 0]) {
                                    rotate (a=90.0, v=[0, 0, -1]) {
                                      rotate (a=90.0, v=[0, 1, 0]) {
                                        translate ([8.575, 0, 0]) {
                                          translate ([9.302129731774905, 0, 0]) {
                                            rotate (a=0.0, v=[1, 0, 0]) {
                                              rotate (a=30.00000000000001, v=[0, -1, 0]) {
                                                translate ([-8.524999999999999, 8.524999999999999, 0]) {
                                                  translate ([0, 0, 1.75]) {
                                                    cube ([0.1, 0.1, 3.5], center=true);
                                                  }
                                                }
                                              }
                                            }
                                          }
                                        }
                                      }
                                    }
                                  }
                                }
                              }
                            }
                            translate ([-35.53437091381005, -63.967580874674, 48.640984358451476]) {
                              rotate (a=-2.5, v=[0, 0, 1]) {
                                rotate (a=-10.0, v=[0, 1, 0]) {
                                  rotate (a=-59.99999999999999, v=[1, 0, 0]) {
                                    rotate (a=90.0, v=[0, 0, -1]) {
                                      rotate (a=90.0, v=[0, 1, 0]) {
                                        translate ([-8.575, 0, 0]) {
                                          translate ([-9.302129731774905, 0, 0]) {
                                            rotate (a=0.0, v=[1, 0, 0]) {
                                              rotate (a=30.00000000000001, v=[0, 1, 0]) {
                                                translate ([8.524999999999999, 8.524999999999999, 0]) {
                                                  translate ([0, 0, 1.75]) {
                                                    cube ([0.1, 0.1, 3.5], center=true);
                                                  }
                                                }
                                              }
                                            }
                                          }
                                        }
                                      }
                                    }
                                  }
                                }
                              }
                            }
                          }
                        }
                        union () {
                          hull () {
                            translate ([-35.53437091381005, -63.967580874674, 48.640984358451476]) {
                              rotate (a=-2.5, v=[0, 0, 1]) {
                                rotate (a=-10.0, v=[0, 1, 0]) {
                                  rotate (a=-59.99999999999999, v=[1, 0, 0]) {
                                    rotate (a=90.0, v=[0, 0, -1]) {
                                      rotate (a=90.0, v=[0, 1, 0]) {
                                        translate ([8.575, 0, 0]) {
                                          translate ([9.302129731774905, 0, 0]) {
                                            rotate (a=0.0, v=[1, 0, 0]) {
                                              rotate (a=30.00000000000001, v=[0, -1, 0]) {
                                                translate ([-8.524999999999999, 8.524999999999999, 0]) {
                                                  translate ([0, 0, 1.75]) {
                                                    cube ([0.1, 0.1, 3.5], center=true);
                                                  }
                                                }
                                              }
                                            }
                                          }
                                        }
                                      }
                                    }
                                  }
                                }
                              }
                            }
                            translate ([-35.53437091381005, -63.967580874674, 48.640984358451476]) {
                              rotate (a=-2.5, v=[0, 0, 1]) {
                                rotate (a=-10.0, v=[0, 1, 0]) {
                                  rotate (a=-59.99999999999999, v=[1, 0, 0]) {
                                    rotate (a=90.0, v=[0, 0, -1]) {
                                      rotate (a=90.0, v=[0, 1, 0]) {
                                        translate ([-8.575, 0, 0]) {
                                          translate ([-9.302129731774905, 0, 0]) {
                                            rotate (a=0.0, v=[1, 0, 0]) {
                                              rotate (a=30.00000000000001, v=[0, 1, 0]) {
                                                translate ([8.524999999999999, 8.524999999999999, 0]) {
                                                  translate ([0, 0, 1.75]) {
                                                    cube ([0.1, 0.1, 3.5], center=true);
                                                  }
                                                }
                                              }
                                            }
                                          }
                                        }
                                      }
                                    }
                                  }
                                }
                              }
                            }
                            translate ([-35.53437091381005, -63.967580874674, 48.640984358451476]) {
                              rotate (a=-2.5, v=[0, 0, 1]) {
                                rotate (a=-10.0, v=[0, 1, 0]) {
                                  rotate (a=-59.99999999999999, v=[1, 0, 0]) {
                                    rotate (a=90.0, v=[0, 0, -1]) {
                                      rotate (a=90.0, v=[0, 1, 0]) {
                                        translate ([0, 13.177145998574055, 15.70391108393905]) {
                                          translate ([8.575, 12.149999999999999, 0]) {
                                            translate ([9.302129731774905, 0, 0]) {
                                              rotate (a=40.0, v=[1, 0, 0]) {
                                                rotate (a=30.00000000000001, v=[0, -1, 0]) {
                                                  translate ([-8.524999999999999, -8.524999999999999, 0]) {
                                                    translate ([0, 0, 1.75]) {
                                                      cube ([0.1, 0.1, 3.5], center=true);
                                                    }
                                                  }
                                                }
                                              }
                                            }
                                          }
                                        }
                                      }
                                    }
                                  }
                                }
                              }
                            }
                          }
                          hull () {
                            translate ([-35.53437091381005, -63.967580874674, 48.640984358451476]) {
                              rotate (a=-2.5, v=[0, 0, 1]) {
                                rotate (a=-10.0, v=[0, 1, 0]) {
                                  rotate (a=-59.99999999999999, v=[1, 0, 0]) {
                                    rotate (a=90.0, v=[0, 0, -1]) {
                                      rotate (a=90.0, v=[0, 1, 0]) {
                                        translate ([-8.575, 0, 0]) {
                                          translate ([-9.302129731774905, 0, 0]) {
                                            rotate (a=0.0, v=[1, 0, 0]) {
                                              rotate (a=30.00000000000001, v=[0, 1, 0]) {
                                                translate ([8.524999999999999, 8.524999999999999, 0]) {
                                                  translate ([0, 0, 1.75]) {
                                                    cube ([0.1, 0.1, 3.5], center=true);
                                                  }
                                                }
                                              }
                                            }
                                          }
                                        }
                                      }
                                    }
                                  }
                                }
                              }
                            }
                            translate ([-35.53437091381005, -63.967580874674, 48.640984358451476]) {
                              rotate (a=-2.5, v=[0, 0, 1]) {
                                rotate (a=-10.0, v=[0, 1, 0]) {
                                  rotate (a=-59.99999999999999, v=[1, 0, 0]) {
                                    rotate (a=90.0, v=[0, 0, -1]) {
                                      rotate (a=90.0, v=[0, 1, 0]) {
                                        translate ([0, 13.177145998574055, 15.70391108393905]) {
                                          translate ([8.575, 12.149999999999999, 0]) {
                                            translate ([9.302129731774905, 0, 0]) {
                                              rotate (a=40.0, v=[1, 0, 0]) {
                                                rotate (a=30.00000000000001, v=[0, -1, 0]) {
                                                  translate ([-8.524999999999999, -8.524999999999999, 0]) {
                                                    translate ([0, 0, 1.75]) {
                                                      cube ([0.1, 0.1, 3.5], center=true);
                                                    }
                                                  }
                                                }
                                              }
                                            }
                                          }
                                        }
                                      }
                                    }
                                  }
                                }
                              }
                            }
                            translate ([-35.53437091381005, -63.967580874674, 48.640984358451476]) {
                              rotate (a=-2.5, v=[0, 0, 1]) {
                                rotate (a=-10.0, v=[0, 1, 0]) {
                                  rotate (a=-59.99999999999999, v=[1, 0, 0]) {
                                    rotate (a=90.0, v=[0, 0, -1]) {
                                      rotate (a=90.0, v=[0, 1, 0]) {
                                        translate ([0, 13.177145998574055, 15.70391108393905]) {
                                          translate ([-8.575, 12.149999999999999, 0]) {
                                            translate ([-9.302129731774905, 0, 0]) {
                                              rotate (a=40.0, v=[1, 0, 0]) {
                                                rotate (a=30.00000000000001, v=[0, 1, 0]) {
                                                  translate ([8.524999999999999, -8.524999999999999, 0]) {
                                                    translate ([0, 0, 1.75]) {
                                                      cube ([0.1, 0.1, 3.5], center=true);
                                                    }
                                                  }
                                                }
                                              }
                                            }
                                          }
                                        }
                                      }
                                    }
                                  }
                                }
                              }
                            }
                          }
                        }
                        union () {
                          hull () {
                            translate ([-35.53437091381005, -63.967580874674, 48.640984358451476]) {
                              rotate (a=-2.5, v=[0, 0, 1]) {
                                rotate (a=-10.0, v=[0, 1, 0]) {
                                  rotate (a=-59.99999999999999, v=[1, 0, 0]) {
                                    rotate (a=90.0, v=[0, 0, -1]) {
                                      rotate (a=90.0, v=[0, 1, 0]) {
                                        translate ([0, 13.177145998574055, 15.70391108393905]) {
                                          translate ([-8.575, 12.149999999999999, 0]) {
                                            translate ([-9.302129731774905, 0, 0]) {
                                              rotate (a=40.0, v=[1, 0, 0]) {
                                                rotate (a=30.00000000000001, v=[0, 1, 0]) {
                                                  translate ([8.524999999999999, -8.524999999999999, 0]) {
                                                    translate ([0, 0, 1.75]) {
                                                      cube ([0.1, 0.1, 3.5], center=true);
                                                    }
                                                  }
                                                }
                                              }
                                            }
                                          }
                                        }
                                      }
                                    }
                                  }
                                }
                              }
                            }
                            translate ([-35.53437091381005, -63.967580874674, 48.640984358451476]) {
                              rotate (a=-2.5, v=[0, 0, 1]) {
                                rotate (a=-10.0, v=[0, 1, 0]) {
                                  rotate (a=-59.99999999999999, v=[1, 0, 0]) {
                                    rotate (a=90.0, v=[0, 0, -1]) {
                                      rotate (a=90.0, v=[0, 1, 0]) {
                                        translate ([-8.575, 0, 0]) {
                                          translate ([-9.302129731774905, 0, 0]) {
                                            rotate (a=0.0, v=[1, 0, 0]) {
                                              rotate (a=30.00000000000001, v=[0, 1, 0]) {
                                                translate ([8.524999999999999, 8.524999999999999, 0]) {
                                                  translate ([0, 0, 1.75]) {
                                                    cube ([0.1, 0.1, 3.5], center=true);
                                                  }
                                                }
                                              }
                                            }
                                          }
                                        }
                                      }
                                    }
                                  }
                                }
                              }
                            }
                            translate ([-35.53437091381005, -63.967580874674, 48.640984358451476]) {
                              rotate (a=-2.5, v=[0, 0, 1]) {
                                rotate (a=-10.0, v=[0, 1, 0]) {
                                  rotate (a=-59.99999999999999, v=[1, 0, 0]) {
                                    rotate (a=90.0, v=[0, 0, -1]) {
                                      rotate (a=90.0, v=[0, 1, 0]) {
                                        translate ([0, 13.177145998574055, 15.70391108393905]) {
                                          translate ([-8.575, 12.149999999999999, 0]) {
                                            translate ([-9.302129731774905, 0, 0]) {
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
